MCMarcusAntony/iBOLIT-2/iBolit-daughter-kicad/iBolit_daughter_v2_f.jpg

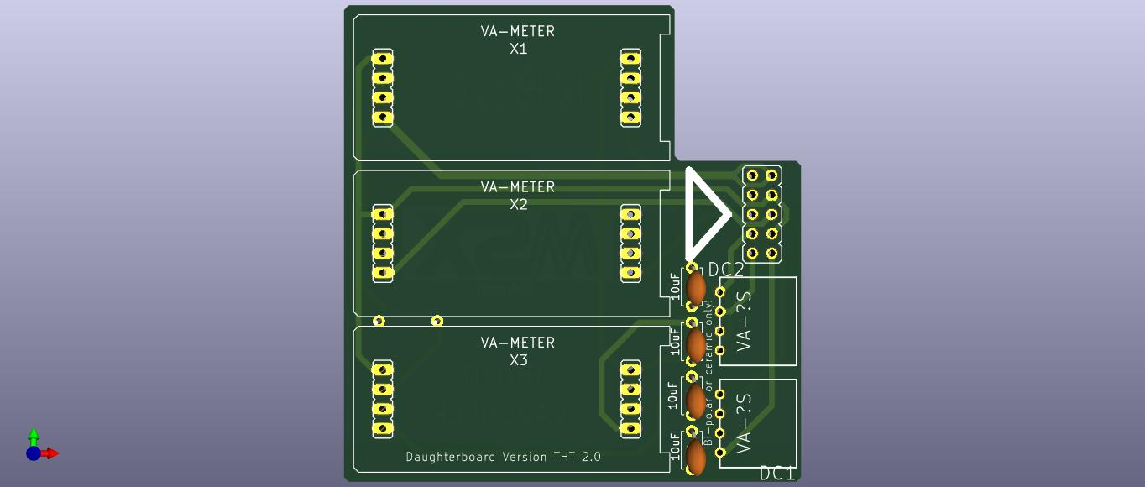
iBolit-daughter-kicad/iBolit_daughter_v2_f.jpg
