MCMarcusAntony/iBOLIT-2/iBolit-kicad/iBolit2.0_main_b.jpg

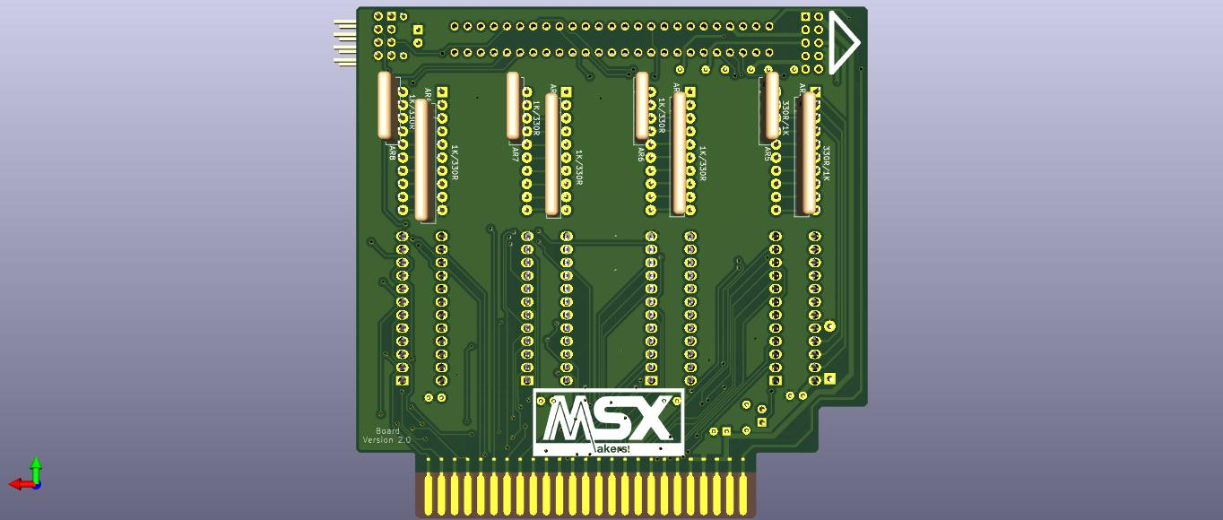
iBolit-kicad/iBolit2.0_main_b.jpg
