MCMarcusAntony/iBOLIT-2/iBolit-ngo-kicad/debounce1d.png

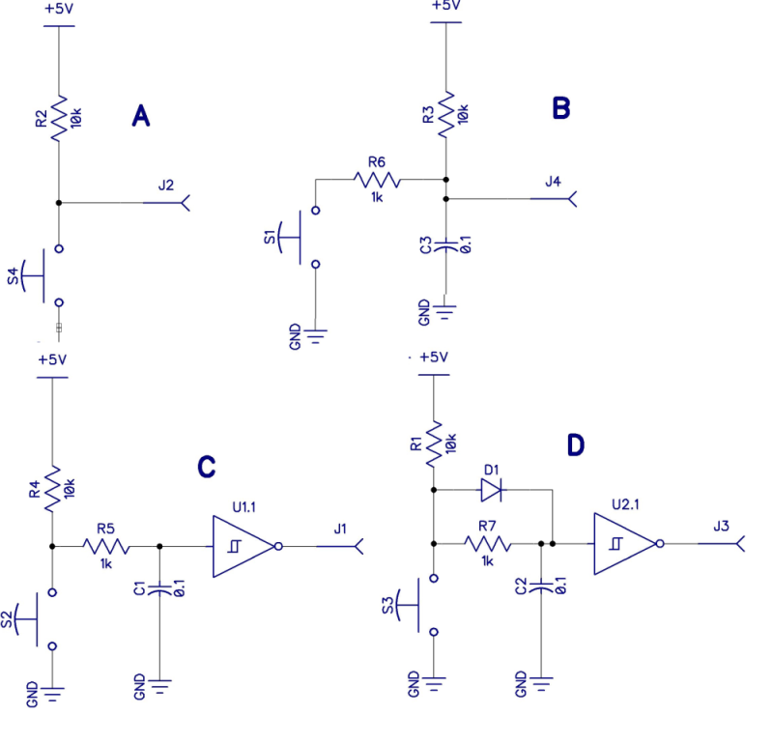
iBolit-ngo-kicad/debounce1d.png
