MCMarcusAntony/iBOLIT-2/iBolit-ngo-kicad/iBolit-ngo-b1.01b.jpg

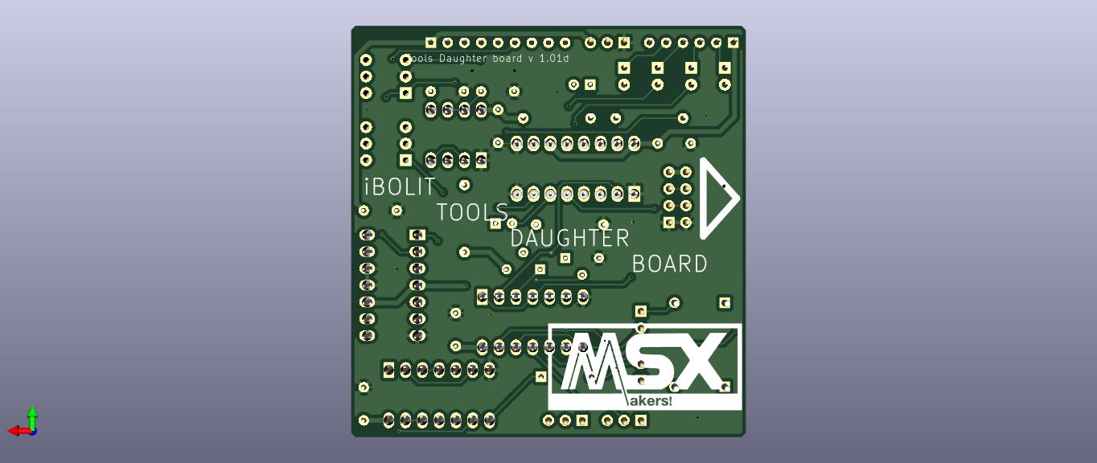
iBolit-ngo-kicad/iBolit-ngo-b1.01b.jpg
