MCMarcusAntony/iBOLIT-2/iBolit-ngo-kicad/single-step-z80.png

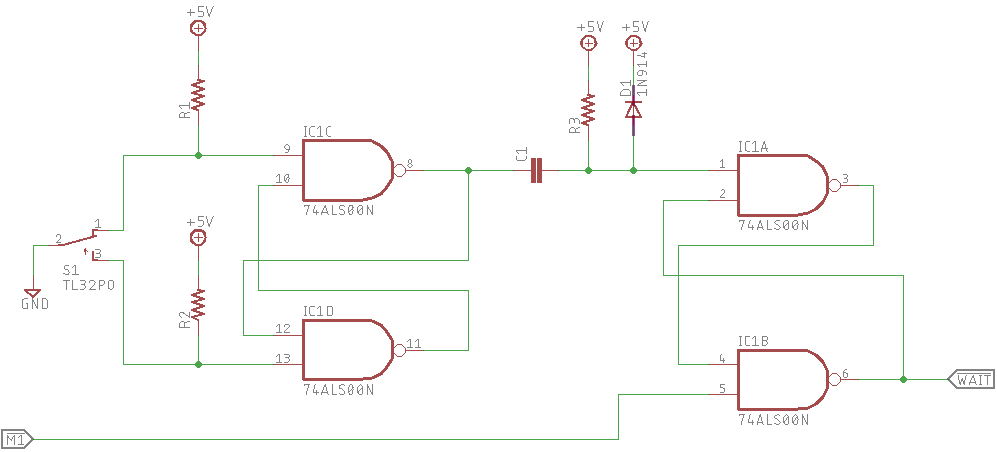
iBolit-ngo-kicad/single-step-z80.png
